alec-chai/stringless-bass/pre-alpha/v0.4.0a-alecgator-rewritten/AcousticBs_samples.cpp

#include "AcousticBs_samples.h"

static const PROGMEM uint32_t sample_0_AcousticBs_ACOBS32A[4224] = {
0xfffb0000,0xfff5fff6,0x004b0004,0x00e5009b,0x01c40151,0x02cf0248,0x03fb0360,0x0539049d,
0x067505d0,0x07b0071a,0x08c70839,0x09af0943,0x0a8a0a12,0x0b220afd,0x0aef0af7,0x0b2d0b26,
0x0a8a0ad9,0x0a4e0a86,0x08760971,0x07b607fa,0x05df06f0,0x047f050a,0x032903ea,0x019d025f,
0x003900e0,0xffdbffd6,0x00a7001e,0x016f011b,0x01af01a4,0x019201a4,0x00ef015d,0xff350029,
0xfd46fe39,0xfbdefc7f,0xfaf6fb58,0xfab7facb,0xfaaafab9,0xfab3fa9f,0xfbbbfb11,0xfd79fc94,
0xff36fe60,0x0148002e,0x02cd0235,0x03620333,0x022f031e,0xff0200b8,0xfd1cfda8,0xfd75fd39,
0xfc65fd4f,0xfa3cfb13,0xf99dfa01,0xf89cf8f5,0xf8def8ce,0xf8def899,0xfc39fa47,0xff7cfdf1,
0x03480149,0x06d6052d,0x09b10846,0x0e490bc1,0x11fd106a,0x165413da,0x1ba2190c,0x1ff31de7,
0x22d5219c,0x246e23bf,0x252a24f8,0x251e2529,0x245424f2,0x2252234d,0x207b2180,0x1dfa1f20,
0x1d401d7c,0x1cfb1cff,0x1e6d1d83,0x1fdc1f4b,0x202c2015,0x21a120a5,0x246e22ef,0x277a2601,
0x295128a6,0x28552943,0x23f82689,0x1cd720ba,0x14b118ba,0x0ce710bb,0x0664095a,0x02bd043b,
0x012301b8,0x011800e6,0x024301a9,0x029602a3,0x0114020e,0xfe53ffc6,0xfb3ffcc2,0xf873f9be,
0xf746f792,0xf8c7f7a9,0xfc61fa69,0x0046fe5c,0x032c01ef,0x02f503a4,0xff83017d,0xfa5dfd2b,
0xf45df748,0xef3df1bf,0xea99ecc4,0xe6b1e8b5,0xe1afe447,0xdca7df18,0xd878da6e,0xd5f7d6f8,
0xd583d57c,0xd6e9d601,0xd980d819,0xdc73dafe,0xdf2fdddf,0xe0b8e01f,0xe161e118,0xe166e185,
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
0xd3fecc2f,0x2c4efc1b,0x1e3d3177,0x1d8c1ee2,0xd595fb36,0xc69fc79e,0x0ffbdb42,0x26c23265,
0x1f7319d3,0xed1011ea,0xcdabd411,0xf19ed071,0x2fd12321,0x20621fd5,0x09902457,0xce45e25b,
0xd413c843,0x290b01fb,0x1655245b,0x17421d0b,0xd8b1f4ef,0xd129d116,0x1ba9ea5e,0x1f16300a,
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
};

static const PROGMEM AudioSynthWavetable::sample_data AcousticBs_samples[6] = {
	{
		(int16_t*)sample_0_AcousticBs_ACOBS32A, // sample
		true, // LOOP
		14, // LENGTH_BITS
		(1 << (32 - 14)) * WAVETABLE_CENTS_SHIFT(0) * 22050.0 / WAVETABLE_NOTE_TO_FREQUENCY(32) / AUDIO_SAMPLE_RATE_EXACT + 0.5, // PER_HERTZ_PHASE_INCREMENT
		((uint32_t)8241 - 1) << (32 - 14), // MAX_PHASE
		((uint32_t)8240 - 1) << (32 - 14), // LOOP_PHASE_END
		(((uint32_t)8240 - 1) << (32 - 14)) - (((uint32_t)7814 - 1) << (32 - 14)), // LOOP_PHASE_LENGTH
		uint16_t(UINT16_MAX * WAVETABLE_DECIBEL_SHIFT(0)), // INITIAL_ATTENUATION_SCALAR
		uint32_t(0.00 * AudioSynthWavetable::SAMPLES_PER_MSEC / AudioSynthWavetable::ENVELOPE_PERIOD + 0.5), // DELAY_COUNT
		uint32_t(1.00 * AudioSynthWavetable::SAMPLES_PER_MSEC / AudioSynthWavetable::ENVELOPE_PERIOD + 0.5), // ATTACK_COUNT
		uint32_t(0.00 * AudioSynthWavetable::SAMPLES_PER_MSEC / AudioSynthWavetable::ENVELOPE_PERIOD + 0.5), // HOLD_COUNT
		uint32_t(4721.24 * AudioSynthWavetable::SAMPLES_PER_MSEC / AudioSynthWavetable::ENVELOPE_PERIOD + 0.5), // DECAY_COUNT
		uint32_t(59.99 * AudioSynthWavetable::SAMPLES_PER_MSEC / AudioSynthWavetable::ENVELOPE_PERIOD + 0.5), // RELEASE_COUNT
		int32_t((1.0 - WAVETABLE_DECIBEL_SHIFT(-2.5)) * AudioSynthWavetable::UNITY_GAIN), // SUSTAIN_MULT
		uint32_t(0.00 * AudioSynthWavetable::SAMPLES_PER_MSEC / (2 * AudioSynthWavetable::LFO_PERIOD)), // VIBRATO_DELAY
		uint32_t(8.2 * AudioSynthWavetable::LFO_PERIOD * (UINT32_MAX / AUDIO_SAMPLE_RATE_EXACT)), // VIBRATO_INCREMENT
		(WAVETABLE_CENTS_SHIFT(0) - 1.0) * 4, // VIBRATO_PITCH_COEFFICIENT_INITIAL
		(1.0 - WAVETABLE_CENTS_SHIFT(0)) * 4, // VIBRATO_COEFFICIENT_SECONDARY
		uint32_t(334.10 * AudioSynthWavetable::SAMPLES_PER_MSEC / (2 * AudioSynthWavetable::LFO_PERIOD)), // MODULATION_DELAY
		uint32_t(6.0 * AudioSynthWavetable::LFO_PERIOD * (UINT32_MAX / AUDIO_SAMPLE_RATE_EXACT)), // MODULATION_INCREMENT
		(WAVETABLE_CENTS_SHIFT(1) - 1.0) * 4, // MODULATION_PITCH_COEFFICIENT_INITIAL
		(1.0 - WAVETABLE_CENTS_SHIFT(-1)) * 4, // MODULATION_PITCH_COEFFICIENT_SECOND
		int32_t(UINT16_MAX * (WAVETABLE_DECIBEL_SHIFT(0) - 1.0)) * 4, // MODULATION_AMPLITUDE_INITIAL_GAIN
		int32_t(UINT16_MAX * (1.0 - WAVETABLE_DECIBEL_SHIFT(0))) * 4, // MODULATION_AMPLITUDE_FINAL_GAIN
	},
	{
		(int16_t*)sample_1_AcousticBs_ACOBS43A, // sample
		true, // LOOP
		13, // LENGTH_BITS
		(1 << (32 - 13)) * WAVETABLE_CENTS_SHIFT(0) * 22050.0 / WAVETABLE_NOTE_TO_FREQUENCY(43) / AUDIO_SAMPLE_RATE_EXACT + 0.5, // PER_HERTZ_PHASE_INCREMENT
		((uint32_t)6991 - 1) << (32 - 13), // MAX_PHASE
		((uint32_t)6990 - 1) << (32 - 13), // LOOP_PHASE_END
		(((uint32_t)6990 - 1) << (32 - 13)) - (((uint32_t)6539 - 1) << (32 - 13)), // LOOP_PHASE_LENGTH
		uint16_t(UINT16_MAX * WAVETABLE_DECIBEL_SHIFT(0)), // INITIAL_ATTENUATION_SCALAR
		uint32_t(0.00 * AudioSynthWavetable::SAMPLES_PER_MSEC / AudioSynthWavetable::ENVELOPE_PERIOD + 0.5), // DELAY_COUNT
		uint32_t(1.00 * AudioSynthWavetable::SAMPLES_PER_MSEC / AudioSynthWavetable::ENVELOPE_PERIOD + 0.5), // ATTACK_COUNT
		uint32_t(0.00 * AudioSynthWavetable::SAMPLES_PER_MSEC / AudioSynthWavetable::ENVELOPE_PERIOD + 0.5), // HOLD_COUNT
		uint32_t(4721.24 * AudioSynthWavetable::SAMPLES_PER_MSEC / AudioSynthWavetable::ENVELOPE_PERIOD + 0.5), // DECAY_COUNT
		uint32_t(59.99 * AudioSynthWavetable::SAMPLES_PER_MSEC / AudioSynthWavetable::ENVELOPE_PERIOD + 0.5), // RELEASE_COUNT
		int32_t((1.0 - WAVETABLE_DECIBEL_SHIFT(-2.5)) * AudioSynthWavetable::UNITY_GAIN), // SUSTAIN_MULT
		uint32_t(0.00 * AudioSynthWavetable::SAMPLES_PER_MSEC / (2 * AudioSynthWavetable::LFO_PERIOD)), // VIBRATO_DELAY
		uint32_t(8.2 * AudioSynthWavetable::LFO_PERIOD * (UINT32_MAX / AUDIO_SAMPLE_RATE_EXACT)), // VIBRATO_INCREMENT
		(WAVETABLE_CENTS_SHIFT(0) - 1.0) * 4, // VIBRATO_PITCH_COEFFICIENT_INITIAL
		(1.0 - WAVETABLE_CENTS_SHIFT(0)) * 4, // VIBRATO_COEFFICIENT_SECONDARY
		uint32_t(334.10 * AudioSynthWavetable::SAMPLES_PER_MSEC / (2 * AudioSynthWavetable::LFO_PERIOD)), // MODULATION_DELAY
		uint32_t(6.0 * AudioSynthWavetable::LFO_PERIOD * (UINT32_MAX / AUDIO_SAMPLE_RATE_EXACT)), // MODULATION_INCREMENT
		(WAVETABLE_CENTS_SHIFT(1) - 1.0) * 4, // MODULATION_PITCH_COEFFICIENT_INITIAL
		(1.0 - WAVETABLE_CENTS_SHIFT(-1)) * 4, // MODULATION_PITCH_COEFFICIENT_SECOND
		int32_t(UINT16_MAX * (WAVETABLE_DECIBEL_SHIFT(0) - 1.0)) * 4, // MODULATION_AMPLITUDE_INITIAL_GAIN
		int32_t(UINT16_MAX * (1.0 - WAVETABLE_DECIBEL_SHIFT(0))) * 4, // MODULATION_AMPLITUDE_FINAL_GAIN
	},
	{
		(int16_t*)sample_2_AcousticBs_ACOBS60A, // sample
		true, // LOOP
		12, // LENGTH_BITS
		(1 << (32 - 12)) * WAVETABLE_CENTS_SHIFT(0) * 22050.0 / WAVETABLE_NOTE_TO_FREQUENCY(60) / AUDIO_SAMPLE_RATE_EXACT + 0.5, // PER_HERTZ_PHASE_INCREMENT
		((uint32_t)2725 - 1) << (32 - 12), // MAX_PHASE
		((uint32_t)2724 - 1) << (32 - 12), // LOOP_PHASE_END
		(((uint32_t)2724 - 1) << (32 - 12)) - (((uint32_t)2639 - 1) << (32 - 12)), // LOOP_PHASE_LENGTH
		uint16_t(UINT16_MAX * WAVETABLE_DECIBEL_SHIFT(0)), // INITIAL_ATTENUATION_SCALAR
		uint32_t(0.00 * AudioSynthWavetable::SAMPLES_PER_MSEC / AudioSynthWavetable::ENVELOPE_PERIOD + 0.5), // DELAY_COUNT
		uint32_t(1.00 * AudioSynthWavetable::SAMPLES_PER_MSEC / AudioSynthWavetable::ENVELOPE_PERIOD + 0.5), // ATTACK_COUNT
		uint32_t(0.00 * AudioSynthWavetable::SAMPLES_PER_MSEC / AudioSynthWavetable::ENVELOPE_PERIOD + 0.5), // HOLD_COUNT
		uint32_t(4721.24 * AudioSynthWavetable::SAMPLES_PER_MSEC / AudioSynthWavetable::ENVELOPE_PERIOD + 0.5), // DECAY_COUNT
		uint32_t(59.99 * AudioSynthWavetable::SAMPLES_PER_MSEC / AudioSynthWavetable::ENVELOPE_PERIOD + 0.5), // RELEASE_COUNT
		int32_t((1.0 - WAVETABLE_DECIBEL_SHIFT(-2.5)) * AudioSynthWavetable::UNITY_GAIN), // SUSTAIN_MULT
		uint32_t(0.00 * AudioSynthWavetable::SAMPLES_PER_MSEC / (2 * AudioSynthWavetable::LFO_PERIOD)), // VIBRATO_DELAY
		uint32_t(8.2 * AudioSynthWavetable::LFO_PERIOD * (UINT32_MAX / AUDIO_SAMPLE_RATE_EXACT)), // VIBRATO_INCREMENT
		(WAVETABLE_CENTS_SHIFT(0) - 1.0) * 4, // VIBRATO_PITCH_COEFFICIENT_INITIAL
		(1.0 - WAVETABLE_CENTS_SHIFT(0)) * 4, // VIBRATO_COEFFICIENT_SECONDARY
		uint32_t(334.10 * AudioSynthWavetable::SAMPLES_PER_MSEC / (2 * AudioSynthWavetable::LFO_PERIOD)), // MODULATION_DELAY
		uint32_t(6.0 * AudioSynthWavetable::LFO_PERIOD * (UINT32_MAX / AUDIO_SAMPLE_RATE_EXACT)), // MODULATION_INCREMENT
		(WAVETABLE_CENTS_SHIFT(1) - 1.0) * 4, // MODULATION_PITCH_COEFFICIENT_INITIAL
		(1.0 - WAVETABLE_CENTS_SHIFT(-1)) * 4, // MODULATION_PITCH_COEFFICIENT_SECOND
		int32_t(UINT16_MAX * (WAVETABLE_DECIBEL_SHIFT(0) - 1.0)) * 4, // MODULATION_AMPLITUDE_INITIAL_GAIN
		int32_t(UINT16_MAX * (1.0 - WAVETABLE_DECIBEL_SHIFT(0))) * 4, // MODULATION_AMPLITUDE_FINAL_GAIN
	},
	{
		(int16_t*)sample_3_AcousticBs_ACOBS60A, // sample
		true, // LOOP
		12, // LENGTH_BITS
		(1 << (32 - 12)) * WAVETABLE_CENTS_SHIFT(0) * 22050.0 / WAVETABLE_NOTE_TO_FREQUENCY(60) / AUDIO_SAMPLE_RATE_EXACT + 0.5, // PER_HERTZ_PHASE_INCREMENT
		((uint32_t)2725 - 1) << (32 - 12), // MAX_PHASE
		((uint32_t)2724 - 1) << (32 - 12), // LOOP_PHASE_END
		(((uint32_t)2724 - 1) << (32 - 12)) - (((uint32_t)2639 - 1) << (32 - 12)), // LOOP_PHASE_LENGTH
		uint16_t(UINT16_MAX * WAVETABLE_DECIBEL_SHIFT(0)), // INITIAL_ATTENUATION_SCALAR
		uint32_t(0.00 * AudioSynthWavetable::SAMPLES_PER_MSEC / AudioSynthWavetable::ENVELOPE_PERIOD + 0.5), // DELAY_COUNT
		uint32_t(1.00 * AudioSynthWavetable::SAMPLES_PER_MSEC / AudioSynthWavetable::ENVELOPE_PERIOD + 0.5), // ATTACK_COUNT
		uint32_t(0.00 * AudioSynthWavetable::SAMPLES_PER_MSEC / AudioSynthWavetable::ENVELOPE_PERIOD + 0.5), // HOLD_COUNT
		uint32_t(4721.24 * AudioSynthWavetable::SAMPLES_PER_MSEC / AudioSynthWavetable::ENVELOPE_PERIOD + 0.5), // DECAY_COUNT
		uint32_t(59.99 * AudioSynthWavetable::SAMPLES_PER_MSEC / AudioSynthWavetable::ENVELOPE_PERIOD + 0.5), // RELEASE_COUNT
		int32_t((1.0 - WAVETABLE_DECIBEL_SHIFT(-2.5)) * AudioSynthWavetable::UNITY_GAIN), // SUSTAIN_MULT
		uint32_t(0.00 * AudioSynthWavetable::SAMPLES_PER_MSEC / (2 * AudioSynthWavetable::LFO_PERIOD)), // VIBRATO_DELAY
		uint32_t(8.2 * AudioSynthWavetable::LFO_PERIOD * (UINT32_MAX / AUDIO_SAMPLE_RATE_EXACT)), // VIBRATO_INCREMENT
		(WAVETABLE_CENTS_SHIFT(0) - 1.0) * 4, // VIBRATO_PITCH_COEFFICIENT_INITIAL
		(1.0 - WAVETABLE_CENTS_SHIFT(0)) * 4, // VIBRATO_COEFFICIENT_SECONDARY
		uint32_t(334.10 * AudioSynthWavetable::SAMPLES_PER_MSEC / (2 * AudioSynthWavetable::LFO_PERIOD)), // MODULATION_DELAY
		uint32_t(6.0 * AudioSynthWavetable::LFO_PERIOD * (UINT32_MAX / AUDIO_SAMPLE_RATE_EXACT)), // MODULATION_INCREMENT
		(WAVETABLE_CENTS_SHIFT(1) - 1.0) * 4, // MODULATION_PITCH_COEFFICIENT_INITIAL
		(1.0 - WAVETABLE_CENTS_SHIFT(-1)) * 4, // MODULATION_PITCH_COEFFICIENT_SECOND
		int32_t(UINT16_MAX * (WAVETABLE_DECIBEL_SHIFT(0) - 1.0)) * 4, // MODULATION_AMPLITUDE_INITIAL_GAIN
		int32_t(UINT16_MAX * (1.0 - WAVETABLE_DECIBEL_SHIFT(0))) * 4, // MODULATION_AMPLITUDE_FINAL_GAIN
	},
	{
		(int16_t*)sample_4_AcousticBs_HARP_83A, // sample
		true, // LOOP
		12, // LENGTH_BITS
		(1 << (32 - 12)) * WAVETABLE_CENTS_SHIFT(0) * 22050.0 / WAVETABLE_NOTE_TO_FREQUENCY(83) / AUDIO_SAMPLE_RATE_EXACT + 0.5, // PER_HERTZ_PHASE_INCREMENT
		((uint32_t)2760 - 1) << (32 - 12), // MAX_PHASE
		((uint32_t)2759 - 1) << (32 - 12), // LOOP_PHASE_END
		(((uint32_t)2759 - 1) << (32 - 12)) - (((uint32_t)2290 - 1) << (32 - 12)), // LOOP_PHASE_LENGTH
		uint16_t(UINT16_MAX * WAVETABLE_DECIBEL_SHIFT(0)), // INITIAL_ATTENUATION_SCALAR
		uint32_t(0.00 * AudioSynthWavetable::SAMPLES_PER_MSEC / AudioSynthWavetable::ENVELOPE_PERIOD + 0.5), // DELAY_COUNT
		uint32_t(1.00 * AudioSynthWavetable::SAMPLES_PER_MSEC / AudioSynthWavetable::ENVELOPE_PERIOD + 0.5), // ATTACK_COUNT
		uint32_t(0.00 * AudioSynthWavetable::SAMPLES_PER_MSEC / AudioSynthWavetable::ENVELOPE_PERIOD + 0.5), // HOLD_COUNT
		uint32_t(4721.24 * AudioSynthWavetable::SAMPLES_PER_MSEC / AudioSynthWavetable::ENVELOPE_PERIOD + 0.5), // DECAY_COUNT
		uint32_t(59.99 * AudioSynthWavetable::SAMPLES_PER_MSEC / AudioSynthWavetable::ENVELOPE_PERIOD + 0.5), // RELEASE_COUNT
		int32_t((1.0 - WAVETABLE_DECIBEL_SHIFT(-2.5)) * AudioSynthWavetable::UNITY_GAIN), // SUSTAIN_MULT
		uint32_t(0.00 * AudioSynthWavetable::SAMPLES_PER_MSEC / (2 * AudioSynthWavetable::LFO_PERIOD)), // VIBRATO_DELAY
		uint32_t(8.2 * AudioSynthWavetable::LFO_PERIOD * (UINT32_MAX / AUDIO_SAMPLE_RATE_EXACT)), // VIBRATO_INCREMENT
		(WAVETABLE_CENTS_SHIFT(0) - 1.0) * 4, // VIBRATO_PITCH_COEFFICIENT_INITIAL
		(1.0 - WAVETABLE_CENTS_SHIFT(0)) * 4, // VIBRATO_COEFFICIENT_SECONDARY
		uint32_t(334.10 * AudioSynthWavetable::SAMPLES_PER_MSEC / (2 * AudioSynthWavetable::LFO_PERIOD)), // MODULATION_DELAY
		uint32_t(6.0 * AudioSynthWavetable::LFO_PERIOD * (UINT32_MAX / AUDIO_SAMPLE_RATE_EXACT)), // MODULATION_INCREMENT
		(WAVETABLE_CENTS_SHIFT(1) - 1.0) * 4, // MODULATION_PITCH_COEFFICIENT_INITIAL
		(1.0 - WAVETABLE_CENTS_SHIFT(-1)) * 4, // MODULATION_PITCH_COEFFICIENT_SECOND
		int32_t(UINT16_MAX * (WAVETABLE_DECIBEL_SHIFT(0) - 1.0)) * 4, // MODULATION_AMPLITUDE_INITIAL_GAIN
		int32_t(UINT16_MAX * (1.0 - WAVETABLE_DECIBEL_SHIFT(0))) * 4, // MODULATION_AMPLITUDE_FINAL_GAIN
	},
	{
		(int16_t*)sample_5_AcousticBs_HARP_96A, // sample
		true, // LOOP
		12, // LENGTH_BITS
		(1 << (32 - 12)) * WAVETABLE_CENTS_SHIFT(0) * 22050.0 / WAVETABLE_NOTE_TO_FREQUENCY(96) / AUDIO_SAMPLE_RATE_EXACT + 0.5, // PER_HERTZ_PHASE_INCREMENT
		((uint32_t)2182 - 1) << (32 - 12), // MAX_PHASE
		((uint32_t)2181 - 1) << (32 - 12), // LOOP_PHASE_END
		(((uint32_t)2181 - 1) << (32 - 12)) - (((uint32_t)2033 - 1) << (32 - 12)), // LOOP_PHASE_LENGTH
		uint16_t(UINT16_MAX * WAVETABLE_DECIBEL_SHIFT(0)), // INITIAL_ATTENUATION_SCALAR
		uint32_t(0.00 * AudioSynthWavetable::SAMPLES_PER_MSEC / AudioSynthWavetable::ENVELOPE_PERIOD + 0.5), // DELAY_COUNT
		uint32_t(1.00 * AudioSynthWavetable::SAMPLES_PER_MSEC / AudioSynthWavetable::ENVELOPE_PERIOD + 0.5), // ATTACK_COUNT
		uint32_t(0.00 * AudioSynthWavetable::SAMPLES_PER_MSEC / AudioSynthWavetable::ENVELOPE_PERIOD + 0.5), // HOLD_COUNT
		uint32_t(4721.24 * AudioSynthWavetable::SAMPLES_PER_MSEC / AudioSynthWavetable::ENVELOPE_PERIOD + 0.5), // DECAY_COUNT
		uint32_t(59.99 * AudioSynthWavetable::SAMPLES_PER_MSEC / AudioSynthWavetable::ENVELOPE_PERIOD + 0.5), // RELEASE_COUNT
		int32_t((1.0 - WAVETABLE_DECIBEL_SHIFT(-2.5)) * AudioSynthWavetable::UNITY_GAIN), // SUSTAIN_MULT
		uint32_t(0.00 * AudioSynthWavetable::SAMPLES_PER_MSEC / (2 * AudioSynthWavetable::LFO_PERIOD)), // VIBRATO_DELAY
		uint32_t(8.2 * AudioSynthWavetable::LFO_PERIOD * (UINT32_MAX / AUDIO_SAMPLE_RATE_EXACT)), // VIBRATO_INCREMENT
		(WAVETABLE_CENTS_SHIFT(0) - 1.0) * 4, // VIBRATO_PITCH_COEFFICIENT_INITIAL
		(1.0 - WAVETABLE_CENTS_SHIFT(0)) * 4, // VIBRATO_COEFFICIENT_SECONDARY
		uint32_t(334.10 * AudioSynthWavetable::SAMPLES_PER_MSEC / (2 * AudioSynthWavetable::LFO_PERIOD)), // MODULATION_DELAY
		uint32_t(6.0 * AudioSynthWavetable::LFO_PERIOD * (UINT32_MAX / AUDIO_SAMPLE_RATE_EXACT)), // MODULATION_INCREMENT
		(WAVETABLE_CENTS_SHIFT(1) - 1.0) * 4, // MODULATION_PITCH_COEFFICIENT_INITIAL
		(1.0 - WAVETABLE_CENTS_SHIFT(-1)) * 4, // MODULATION_PITCH_COEFFICIENT_SECOND
		int32_t(UINT16_MAX * (WAVETABLE_DECIBEL_SHIFT(0) - 1.0)) * 4, // MODULATION_AMPLITUDE_INITIAL_GAIN
		int32_t(UINT16_MAX * (1.0 - WAVETABLE_DECIBEL_SHIFT(0))) * 4, // MODULATION_AMPLITUDE_FINAL_GAIN
	},
};

static const PROGMEM uint8_t AcousticBs_ranges[] = {37, 51, 72, 84, 86, 127, };

const PROGMEM AudioSynthWavetable::instrument_data AcousticBs = {6, AcousticBs_ranges, AcousticBs_samples };
