alec-chai/stringless-bass/pre-alpha/v0.4.0a-alecgator-rewritten/PickedBs_samples.cpp

#include "PickedBs_samples.h"

static const PROGMEM uint32_t sample_0_PickedBs_PCKBS30A[3712] = {
0xff730000,0xff2aff3a,0xff56ff31,0xffb4ff8c,0xfffdffe1,0x00230011,0x0039002e,0x00590049,
0x00690061,0x0062006a,0x0045005d,0x001a002d,0xfff40003,0xffc5ffdf,0xff9fffb2,0xff7bff93,
0xff6bff78,0xff68ff6a,0xff7dff74,0xff8bff8d,0xff8eff9b,0xff8fffa2,0x02840093,0x0439036e,
0x059804dc,0x07240657,0x089407e9,0x098f091d,0x0a4809ee,0x0b1d0aa8,0x0e6b0c6e,0x0f4c0f62,
0x0d040e5d,0x09240b43,0x03650677,0xfcf6fffc,0xfa2ffae0,0xfd59fb05,0x052e00dd,0x0e0a09b3,
0x13ed1192,0x143614ce,0x0f791251,0x08800c05,0x0256052e,0xfe7c000b,0xfb0dfd48,0xeb8ef5a7,
0xd370de56,0xddb3d1bc,0x1200f5e0,0x26b325a5,0xef67127d,0xb1d4cabd,0xb8e0ac63,0xe27ece84,
0xeb72ed0e,0xcefadfa5,0xb63abf78,0xbc86b57f,0xd51ac85d,0xe561df86,0xe172e5ca,0xd287da34,
0xca21cca9,0xcee6cb21,0xd84ad3d5,0xdc57db33,0xddc6dcb6,0xe62be0e0,0xf178ec61,0xf341f3db,
0xef79f0fc,0xf5d8f0c9,0x07dcfe1b,0x17f410f9,0x1dfa1c37,0x1c971dd2,0x19f51b15,0x1a9219ad,
0x20e01cef,0x2d47265a,0x3dce3552,0x4bee45a2,0x520a5010,0x50ce5221,0x4c5f4eae,0x4acd4ad4,
0x51374cf2,0x5d0b56f3,0x65df624b,0x6793678d,0x6507668b,0x61ba6359,0x5f6b605d,0x5f9a5f25,
0x61df60aa,0x62b462b8,0x5f2f617e,0x58505c02,0x50ae5477,0x49df4d16,0x44fb471c,0x423b4372,
0x3ee440e1,0x37f23be9,0x2e303349,0x2453290e,0x1cb1202e,0x172b19c8,0x11e2149c,0x0b400ed1,
0x02830722,0xf88efd86,0xefeff3ed,0xea59ecc4,0xe61ee84d,0xdfc1e353,0xd72ddb9f,0xcf80d30a,
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
0xcc4afb85,0xd40bbc09,0x337505f4,0x267940fa,0xc6c5f38f,0xd7b6bb50,0x36af0b34,0x22bf4066,
0xc5faef7f,0xdfa4bf54,0x3cb813c6,0x20cc4202,0xc668ed0a,0xe793c40b,0x41381bc9,0x1ca04184,
0xc41ee83b,0xeb88c593,0x405f1ee4,0x13a03bc5,0xbf0edf91,0xee5fc541,0x3fe0218c,0x0c5d3736,
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
};

static const PROGMEM AudioSynthWavetable::sample_data PickedBs_samples[6] = {
	{
		(int16_t*)sample_0_PickedBs_PCKBS30A, // sample
		true, // LOOP
		13, // LENGTH_BITS
		(1 << (32 - 13)) * WAVETABLE_CENTS_SHIFT(0) * 22050.0 / WAVETABLE_NOTE_TO_FREQUENCY(30) / AUDIO_SAMPLE_RATE_EXACT + 0.5, // PER_HERTZ_PHASE_INCREMENT
		((uint32_t)7171 - 1) << (32 - 13), // MAX_PHASE
		((uint32_t)7170 - 1) << (32 - 13), // LOOP_PHASE_END
		(((uint32_t)7170 - 1) << (32 - 13)) - (((uint32_t)6692 - 1) << (32 - 13)), // LOOP_PHASE_LENGTH
		uint16_t(UINT16_MAX * WAVETABLE_DECIBEL_SHIFT(0)), // INITIAL_ATTENUATION_SCALAR
		uint32_t(0.00 * AudioSynthWavetable::SAMPLES_PER_MSEC / AudioSynthWavetable::ENVELOPE_PERIOD + 0.5), // DELAY_COUNT
		uint32_t(1.00 * AudioSynthWavetable::SAMPLES_PER_MSEC / AudioSynthWavetable::ENVELOPE_PERIOD + 0.5), // ATTACK_COUNT
		uint32_t(0.00 * AudioSynthWavetable::SAMPLES_PER_MSEC / AudioSynthWavetable::ENVELOPE_PERIOD + 0.5), // HOLD_COUNT
		uint32_t(4430.59 * AudioSynthWavetable::SAMPLES_PER_MSEC / AudioSynthWavetable::ENVELOPE_PERIOD + 0.5), // DECAY_COUNT
		uint32_t(29.99 * AudioSynthWavetable::SAMPLES_PER_MSEC / AudioSynthWavetable::ENVELOPE_PERIOD + 0.5), // RELEASE_COUNT
		int32_t((1.0 - WAVETABLE_DECIBEL_SHIFT(-1.6)) * AudioSynthWavetable::UNITY_GAIN), // SUSTAIN_MULT
		uint32_t(0.00 * AudioSynthWavetable::SAMPLES_PER_MSEC / (2 * AudioSynthWavetable::LFO_PERIOD)), // VIBRATO_DELAY
		uint32_t(8.2 * AudioSynthWavetable::LFO_PERIOD * (UINT32_MAX / AUDIO_SAMPLE_RATE_EXACT)), // VIBRATO_INCREMENT
		(WAVETABLE_CENTS_SHIFT(0) - 1.0) * 4, // VIBRATO_PITCH_COEFFICIENT_INITIAL
		(1.0 - WAVETABLE_CENTS_SHIFT(0)) * 4, // VIBRATO_COEFFICIENT_SECONDARY
		uint32_t(334.10 * AudioSynthWavetable::SAMPLES_PER_MSEC / (2 * AudioSynthWavetable::LFO_PERIOD)), // MODULATION_DELAY
		uint32_t(6.0 * AudioSynthWavetable::LFO_PERIOD * (UINT32_MAX / AUDIO_SAMPLE_RATE_EXACT)), // MODULATION_INCREMENT
		(WAVETABLE_CENTS_SHIFT(1) - 1.0) * 4, // MODULATION_PITCH_COEFFICIENT_INITIAL
		(1.0 - WAVETABLE_CENTS_SHIFT(-1)) * 4, // MODULATION_PITCH_COEFFICIENT_SECOND
		int32_t(UINT16_MAX * (WAVETABLE_DECIBEL_SHIFT(0) - 1.0)) * 4, // MODULATION_AMPLITUDE_INITIAL_GAIN
		int32_t(UINT16_MAX * (1.0 - WAVETABLE_DECIBEL_SHIFT(0))) * 4, // MODULATION_AMPLITUDE_FINAL_GAIN
	},
	{
		(int16_t*)sample_1_PickedBs_PCKBS40A, // sample
		true, // LOOP
		13, // LENGTH_BITS
		(1 << (32 - 13)) * WAVETABLE_CENTS_SHIFT(0) * 22050.0 / WAVETABLE_NOTE_TO_FREQUENCY(40) / AUDIO_SAMPLE_RATE_EXACT + 0.5, // PER_HERTZ_PHASE_INCREMENT
		((uint32_t)6837 - 1) << (32 - 13), // MAX_PHASE
		((uint32_t)6836 - 1) << (32 - 13), // LOOP_PHASE_END
		(((uint32_t)6836 - 1) << (32 - 13)) - (((uint32_t)6302 - 1) << (32 - 13)), // LOOP_PHASE_LENGTH
		uint16_t(UINT16_MAX * WAVETABLE_DECIBEL_SHIFT(0)), // INITIAL_ATTENUATION_SCALAR
		uint32_t(0.00 * AudioSynthWavetable::SAMPLES_PER_MSEC / AudioSynthWavetable::ENVELOPE_PERIOD + 0.5), // DELAY_COUNT
		uint32_t(1.00 * AudioSynthWavetable::SAMPLES_PER_MSEC / AudioSynthWavetable::ENVELOPE_PERIOD + 0.5), // ATTACK_COUNT
		uint32_t(0.00 * AudioSynthWavetable::SAMPLES_PER_MSEC / AudioSynthWavetable::ENVELOPE_PERIOD + 0.5), // HOLD_COUNT
		uint32_t(4430.59 * AudioSynthWavetable::SAMPLES_PER_MSEC / AudioSynthWavetable::ENVELOPE_PERIOD + 0.5), // DECAY_COUNT
		uint32_t(29.99 * AudioSynthWavetable::SAMPLES_PER_MSEC / AudioSynthWavetable::ENVELOPE_PERIOD + 0.5), // RELEASE_COUNT
		int32_t((1.0 - WAVETABLE_DECIBEL_SHIFT(-1.6)) * AudioSynthWavetable::UNITY_GAIN), // SUSTAIN_MULT
		uint32_t(0.00 * AudioSynthWavetable::SAMPLES_PER_MSEC / (2 * AudioSynthWavetable::LFO_PERIOD)), // VIBRATO_DELAY
		uint32_t(8.2 * AudioSynthWavetable::LFO_PERIOD * (UINT32_MAX / AUDIO_SAMPLE_RATE_EXACT)), // VIBRATO_INCREMENT
		(WAVETABLE_CENTS_SHIFT(0) - 1.0) * 4, // VIBRATO_PITCH_COEFFICIENT_INITIAL
		(1.0 - WAVETABLE_CENTS_SHIFT(0)) * 4, // VIBRATO_COEFFICIENT_SECONDARY
		uint32_t(334.10 * AudioSynthWavetable::SAMPLES_PER_MSEC / (2 * AudioSynthWavetable::LFO_PERIOD)), // MODULATION_DELAY
		uint32_t(6.0 * AudioSynthWavetable::LFO_PERIOD * (UINT32_MAX / AUDIO_SAMPLE_RATE_EXACT)), // MODULATION_INCREMENT
		(WAVETABLE_CENTS_SHIFT(1) - 1.0) * 4, // MODULATION_PITCH_COEFFICIENT_INITIAL
		(1.0 - WAVETABLE_CENTS_SHIFT(-1)) * 4, // MODULATION_PITCH_COEFFICIENT_SECOND
		int32_t(UINT16_MAX * (WAVETABLE_DECIBEL_SHIFT(0) - 1.0)) * 4, // MODULATION_AMPLITUDE_INITIAL_GAIN
		int32_t(UINT16_MAX * (1.0 - WAVETABLE_DECIBEL_SHIFT(0))) * 4, // MODULATION_AMPLITUDE_FINAL_GAIN
	},
	{
		(int16_t*)sample_2_PickedBs_PCKBS50A, // sample
		true, // LOOP
		12, // LENGTH_BITS
		(1 << (32 - 12)) * WAVETABLE_CENTS_SHIFT(0) * 22050.0 / WAVETABLE_NOTE_TO_FREQUENCY(50) / AUDIO_SAMPLE_RATE_EXACT + 0.5, // PER_HERTZ_PHASE_INCREMENT
		((uint32_t)3699 - 1) << (32 - 12), // MAX_PHASE
		((uint32_t)3698 - 1) << (32 - 12), // LOOP_PHASE_END
		(((uint32_t)3698 - 1) << (32 - 12)) - (((uint32_t)3397 - 1) << (32 - 12)), // LOOP_PHASE_LENGTH
		uint16_t(UINT16_MAX * WAVETABLE_DECIBEL_SHIFT(0)), // INITIAL_ATTENUATION_SCALAR
		uint32_t(0.00 * AudioSynthWavetable::SAMPLES_PER_MSEC / AudioSynthWavetable::ENVELOPE_PERIOD + 0.5), // DELAY_COUNT
		uint32_t(1.00 * AudioSynthWavetable::SAMPLES_PER_MSEC / AudioSynthWavetable::ENVELOPE_PERIOD + 0.5), // ATTACK_COUNT
		uint32_t(0.00 * AudioSynthWavetable::SAMPLES_PER_MSEC / AudioSynthWavetable::ENVELOPE_PERIOD + 0.5), // HOLD_COUNT
		uint32_t(4430.59 * AudioSynthWavetable::SAMPLES_PER_MSEC / AudioSynthWavetable::ENVELOPE_PERIOD + 0.5), // DECAY_COUNT
		uint32_t(29.99 * AudioSynthWavetable::SAMPLES_PER_MSEC / AudioSynthWavetable::ENVELOPE_PERIOD + 0.5), // RELEASE_COUNT
		int32_t((1.0 - WAVETABLE_DECIBEL_SHIFT(-1.6)) * AudioSynthWavetable::UNITY_GAIN), // SUSTAIN_MULT
		uint32_t(0.00 * AudioSynthWavetable::SAMPLES_PER_MSEC / (2 * AudioSynthWavetable::LFO_PERIOD)), // VIBRATO_DELAY
		uint32_t(8.2 * AudioSynthWavetable::LFO_PERIOD * (UINT32_MAX / AUDIO_SAMPLE_RATE_EXACT)), // VIBRATO_INCREMENT
		(WAVETABLE_CENTS_SHIFT(0) - 1.0) * 4, // VIBRATO_PITCH_COEFFICIENT_INITIAL
		(1.0 - WAVETABLE_CENTS_SHIFT(0)) * 4, // VIBRATO_COEFFICIENT_SECONDARY
		uint32_t(334.10 * AudioSynthWavetable::SAMPLES_PER_MSEC / (2 * AudioSynthWavetable::LFO_PERIOD)), // MODULATION_DELAY
		uint32_t(6.0 * AudioSynthWavetable::LFO_PERIOD * (UINT32_MAX / AUDIO_SAMPLE_RATE_EXACT)), // MODULATION_INCREMENT
		(WAVETABLE_CENTS_SHIFT(1) - 1.0) * 4, // MODULATION_PITCH_COEFFICIENT_INITIAL
		(1.0 - WAVETABLE_CENTS_SHIFT(-1)) * 4, // MODULATION_PITCH_COEFFICIENT_SECOND
		int32_t(UINT16_MAX * (WAVETABLE_DECIBEL_SHIFT(0) - 1.0)) * 4, // MODULATION_AMPLITUDE_INITIAL_GAIN
		int32_t(UINT16_MAX * (1.0 - WAVETABLE_DECIBEL_SHIFT(0))) * 4, // MODULATION_AMPLITUDE_FINAL_GAIN
	},
	{
		(int16_t*)sample_3_PickedBs_JAZGT84A, // sample
		true, // LOOP
		13, // LENGTH_BITS
		(1 << (32 - 13)) * WAVETABLE_CENTS_SHIFT(0) * 22050.0 / WAVETABLE_NOTE_TO_FREQUENCY(84) / AUDIO_SAMPLE_RATE_EXACT + 0.5, // PER_HERTZ_PHASE_INCREMENT
		((uint32_t)4989 - 1) << (32 - 13), // MAX_PHASE
		((uint32_t)4988 - 1) << (32 - 13), // LOOP_PHASE_END
		(((uint32_t)4988 - 1) << (32 - 13)) - (((uint32_t)4102 - 1) << (32 - 13)), // LOOP_PHASE_LENGTH
		uint16_t(UINT16_MAX * WAVETABLE_DECIBEL_SHIFT(0)), // INITIAL_ATTENUATION_SCALAR
		uint32_t(0.00 * AudioSynthWavetable::SAMPLES_PER_MSEC / AudioSynthWavetable::ENVELOPE_PERIOD + 0.5), // DELAY_COUNT
		uint32_t(1.00 * AudioSynthWavetable::SAMPLES_PER_MSEC / AudioSynthWavetable::ENVELOPE_PERIOD + 0.5), // ATTACK_COUNT
		uint32_t(0.00 * AudioSynthWavetable::SAMPLES_PER_MSEC / AudioSynthWavetable::ENVELOPE_PERIOD + 0.5), // HOLD_COUNT
		uint32_t(4430.59 * AudioSynthWavetable::SAMPLES_PER_MSEC / AudioSynthWavetable::ENVELOPE_PERIOD + 0.5), // DECAY_COUNT
		uint32_t(29.99 * AudioSynthWavetable::SAMPLES_PER_MSEC / AudioSynthWavetable::ENVELOPE_PERIOD + 0.5), // RELEASE_COUNT
		int32_t((1.0 - WAVETABLE_DECIBEL_SHIFT(-1.6)) * AudioSynthWavetable::UNITY_GAIN), // SUSTAIN_MULT
		uint32_t(0.00 * AudioSynthWavetable::SAMPLES_PER_MSEC / (2 * AudioSynthWavetable::LFO_PERIOD)), // VIBRATO_DELAY
		uint32_t(8.2 * AudioSynthWavetable::LFO_PERIOD * (UINT32_MAX / AUDIO_SAMPLE_RATE_EXACT)), // VIBRATO_INCREMENT
		(WAVETABLE_CENTS_SHIFT(0) - 1.0) * 4, // VIBRATO_PITCH_COEFFICIENT_INITIAL
		(1.0 - WAVETABLE_CENTS_SHIFT(0)) * 4, // VIBRATO_COEFFICIENT_SECONDARY
		uint32_t(334.10 * AudioSynthWavetable::SAMPLES_PER_MSEC / (2 * AudioSynthWavetable::LFO_PERIOD)), // MODULATION_DELAY
		uint32_t(6.0 * AudioSynthWavetable::LFO_PERIOD * (UINT32_MAX / AUDIO_SAMPLE_RATE_EXACT)), // MODULATION_INCREMENT
		(WAVETABLE_CENTS_SHIFT(1) - 1.0) * 4, // MODULATION_PITCH_COEFFICIENT_INITIAL
		(1.0 - WAVETABLE_CENTS_SHIFT(-1)) * 4, // MODULATION_PITCH_COEFFICIENT_SECOND
		int32_t(UINT16_MAX * (WAVETABLE_DECIBEL_SHIFT(0) - 1.0)) * 4, // MODULATION_AMPLITUDE_INITIAL_GAIN
		int32_t(UINT16_MAX * (1.0 - WAVETABLE_DECIBEL_SHIFT(0))) * 4, // MODULATION_AMPLITUDE_FINAL_GAIN
	},
	{
		(int16_t*)sample_4_PickedBs_JAZGT93A, // sample
		true, // LOOP
		12, // LENGTH_BITS
		(1 << (32 - 12)) * WAVETABLE_CENTS_SHIFT(0) * 22050.0 / WAVETABLE_NOTE_TO_FREQUENCY(93) / AUDIO_SAMPLE_RATE_EXACT + 0.5, // PER_HERTZ_PHASE_INCREMENT
		((uint32_t)3560 - 1) << (32 - 12), // MAX_PHASE
		((uint32_t)3559 - 1) << (32 - 12), // LOOP_PHASE_END
		(((uint32_t)3559 - 1) << (32 - 12)) - (((uint32_t)2882 - 1) << (32 - 12)), // LOOP_PHASE_LENGTH
		uint16_t(UINT16_MAX * WAVETABLE_DECIBEL_SHIFT(0)), // INITIAL_ATTENUATION_SCALAR
		uint32_t(0.00 * AudioSynthWavetable::SAMPLES_PER_MSEC / AudioSynthWavetable::ENVELOPE_PERIOD + 0.5), // DELAY_COUNT
		uint32_t(1.00 * AudioSynthWavetable::SAMPLES_PER_MSEC / AudioSynthWavetable::ENVELOPE_PERIOD + 0.5), // ATTACK_COUNT
		uint32_t(0.00 * AudioSynthWavetable::SAMPLES_PER_MSEC / AudioSynthWavetable::ENVELOPE_PERIOD + 0.5), // HOLD_COUNT
		uint32_t(4430.59 * AudioSynthWavetable::SAMPLES_PER_MSEC / AudioSynthWavetable::ENVELOPE_PERIOD + 0.5), // DECAY_COUNT
		uint32_t(29.99 * AudioSynthWavetable::SAMPLES_PER_MSEC / AudioSynthWavetable::ENVELOPE_PERIOD + 0.5), // RELEASE_COUNT
		int32_t((1.0 - WAVETABLE_DECIBEL_SHIFT(-1.6)) * AudioSynthWavetable::UNITY_GAIN), // SUSTAIN_MULT
		uint32_t(0.00 * AudioSynthWavetable::SAMPLES_PER_MSEC / (2 * AudioSynthWavetable::LFO_PERIOD)), // VIBRATO_DELAY
		uint32_t(8.2 * AudioSynthWavetable::LFO_PERIOD * (UINT32_MAX / AUDIO_SAMPLE_RATE_EXACT)), // VIBRATO_INCREMENT
		(WAVETABLE_CENTS_SHIFT(0) - 1.0) * 4, // VIBRATO_PITCH_COEFFICIENT_INITIAL
		(1.0 - WAVETABLE_CENTS_SHIFT(0)) * 4, // VIBRATO_COEFFICIENT_SECONDARY
		uint32_t(334.10 * AudioSynthWavetable::SAMPLES_PER_MSEC / (2 * AudioSynthWavetable::LFO_PERIOD)), // MODULATION_DELAY
		uint32_t(6.0 * AudioSynthWavetable::LFO_PERIOD * (UINT32_MAX / AUDIO_SAMPLE_RATE_EXACT)), // MODULATION_INCREMENT
		(WAVETABLE_CENTS_SHIFT(1) - 1.0) * 4, // MODULATION_PITCH_COEFFICIENT_INITIAL
		(1.0 - WAVETABLE_CENTS_SHIFT(-1)) * 4, // MODULATION_PITCH_COEFFICIENT_SECOND
		int32_t(UINT16_MAX * (WAVETABLE_DECIBEL_SHIFT(0) - 1.0)) * 4, // MODULATION_AMPLITUDE_INITIAL_GAIN
		int32_t(UINT16_MAX * (1.0 - WAVETABLE_DECIBEL_SHIFT(0))) * 4, // MODULATION_AMPLITUDE_FINAL_GAIN
	},
	{
		(int16_t*)sample_5_PickedBs_JAZGTA1A, // sample
		true, // LOOP
		12, // LENGTH_BITS
		(1 << (32 - 12)) * WAVETABLE_CENTS_SHIFT(0) * 22050.0 / WAVETABLE_NOTE_TO_FREQUENCY(101) / AUDIO_SAMPLE_RATE_EXACT + 0.5, // PER_HERTZ_PHASE_INCREMENT
		((uint32_t)2491 - 1) << (32 - 12), // MAX_PHASE
		((uint32_t)2490 - 1) << (32 - 12), // LOOP_PHASE_END
		(((uint32_t)2490 - 1) << (32 - 12)) - (((uint32_t)1843 - 1) << (32 - 12)), // LOOP_PHASE_LENGTH
		uint16_t(UINT16_MAX * WAVETABLE_DECIBEL_SHIFT(0)), // INITIAL_ATTENUATION_SCALAR
		uint32_t(0.00 * AudioSynthWavetable::SAMPLES_PER_MSEC / AudioSynthWavetable::ENVELOPE_PERIOD + 0.5), // DELAY_COUNT
		uint32_t(1.00 * AudioSynthWavetable::SAMPLES_PER_MSEC / AudioSynthWavetable::ENVELOPE_PERIOD + 0.5), // ATTACK_COUNT
		uint32_t(0.00 * AudioSynthWavetable::SAMPLES_PER_MSEC / AudioSynthWavetable::ENVELOPE_PERIOD + 0.5), // HOLD_COUNT
		uint32_t(4430.59 * AudioSynthWavetable::SAMPLES_PER_MSEC / AudioSynthWavetable::ENVELOPE_PERIOD + 0.5), // DECAY_COUNT
		uint32_t(29.99 * AudioSynthWavetable::SAMPLES_PER_MSEC / AudioSynthWavetable::ENVELOPE_PERIOD + 0.5), // RELEASE_COUNT
		int32_t((1.0 - WAVETABLE_DECIBEL_SHIFT(-1.6)) * AudioSynthWavetable::UNITY_GAIN), // SUSTAIN_MULT
		uint32_t(0.00 * AudioSynthWavetable::SAMPLES_PER_MSEC / (2 * AudioSynthWavetable::LFO_PERIOD)), // VIBRATO_DELAY
		uint32_t(8.2 * AudioSynthWavetable::LFO_PERIOD * (UINT32_MAX / AUDIO_SAMPLE_RATE_EXACT)), // VIBRATO_INCREMENT
		(WAVETABLE_CENTS_SHIFT(0) - 1.0) * 4, // VIBRATO_PITCH_COEFFICIENT_INITIAL
		(1.0 - WAVETABLE_CENTS_SHIFT(0)) * 4, // VIBRATO_COEFFICIENT_SECONDARY
		uint32_t(334.10 * AudioSynthWavetable::SAMPLES_PER_MSEC / (2 * AudioSynthWavetable::LFO_PERIOD)), // MODULATION_DELAY
		uint32_t(6.0 * AudioSynthWavetable::LFO_PERIOD * (UINT32_MAX / AUDIO_SAMPLE_RATE_EXACT)), // MODULATION_INCREMENT
		(WAVETABLE_CENTS_SHIFT(1) - 1.0) * 4, // MODULATION_PITCH_COEFFICIENT_INITIAL
		(1.0 - WAVETABLE_CENTS_SHIFT(-1)) * 4, // MODULATION_PITCH_COEFFICIENT_SECOND
		int32_t(UINT16_MAX * (WAVETABLE_DECIBEL_SHIFT(0) - 1.0)) * 4, // MODULATION_AMPLITUDE_INITIAL_GAIN
		int32_t(UINT16_MAX * (1.0 - WAVETABLE_DECIBEL_SHIFT(0))) * 4, // MODULATION_AMPLITUDE_FINAL_GAIN
	},
};

static const PROGMEM uint8_t PickedBs_ranges[] = {35, 45, 78, 88, 97, 127, };

const PROGMEM AudioSynthWavetable::instrument_data PickedBs = {6, PickedBs_ranges, PickedBs_samples };
